g2maurer/PowerMonitor_V7_2/Images/PCB_back.jpg

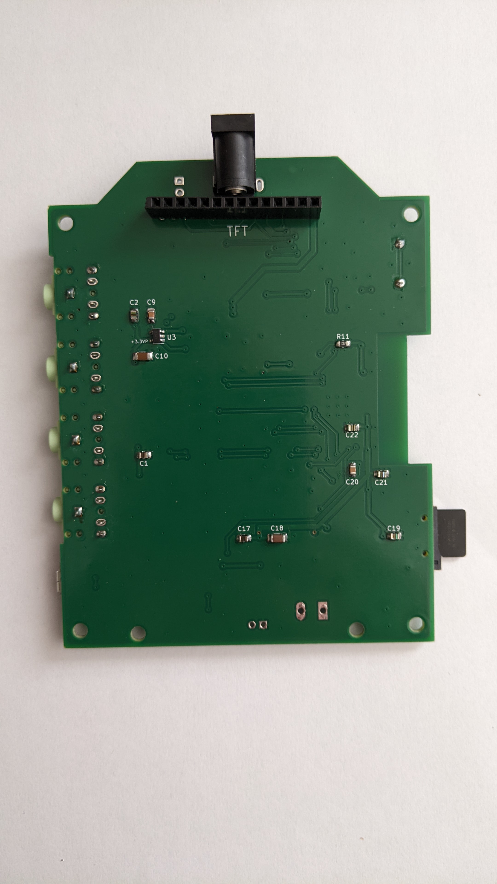
Images/PCB_back.jpg
