g2maurer/PowerMonitor_V7_2/Images/PCB_in_Enclosure.jpg

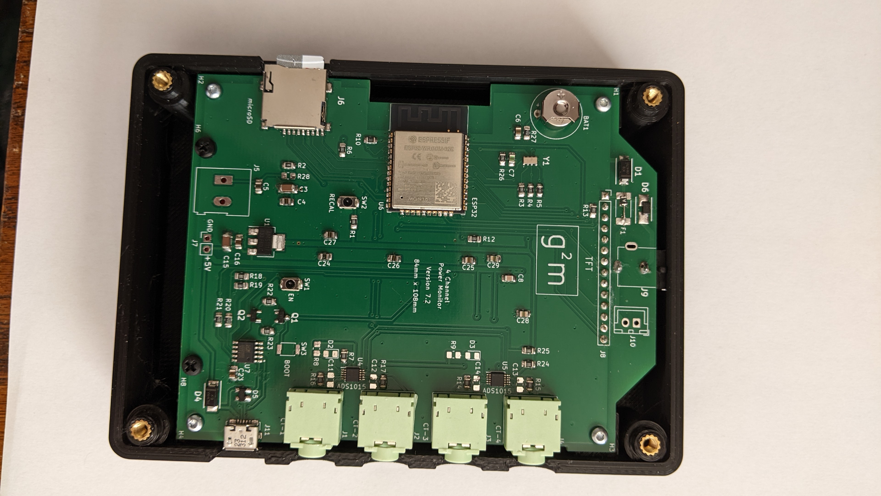
Images/PCB_in_Enclosure.jpg
