g2maurer/PowerMonitor_V7_2/Images/SD_slot.jpg

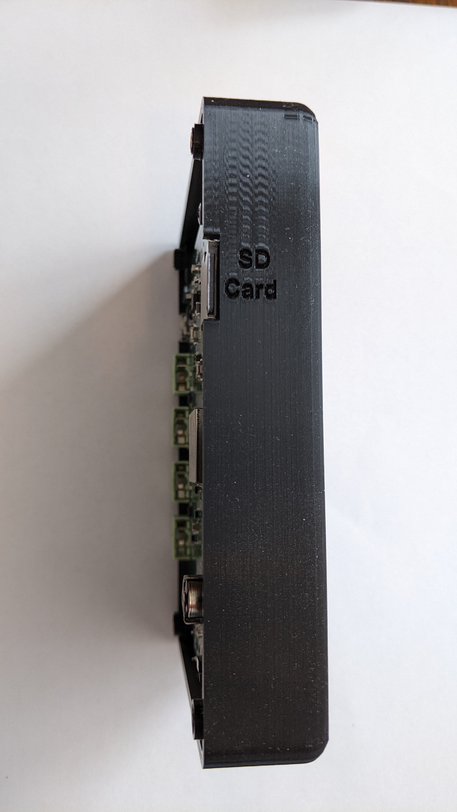
Images/SD_slot.jpg
