g2maurer/PowerMonitor_V7_2/Code/FileHandler.ino

///////////////////////////////////
//
//    Determines whether File exists
//
boolean existsFile(fs::FS &fs, const char *fileName)
{
  return fs.exists(fileName);
}

///////////////////////////////////////////////////////////
//
// Write to the SD card (DON'T MODIFY THIS FUNCTION)
//
//  Example:    writeFile(SD, "/data.txt", "Reading ID, Date, Hour, Temperature \r\n");
//
//
void writeFile(fs::FS &fs, const char * path, const char * message) {
  Serial.printf("Writing file: %s\n", path);

  File file = fs.open(path, FILE_WRITE);
  if(!file) {
    Serial.println("Failed to open file for writing");
    return;
  }
  if(file.print(message)) {
    Serial.println("File written");
  } else {
    Serial.println("Write failed");
  }
  file.close();
}

///////////////////////////////////////////////////////////
//
// Append data to the SD card (DON'T MODIFY THIS FUNCTION)
//
//  Example:    appendFile(SD, "/data.txt", dataMessage.c_str());
//
void appendFile(fs::FS &fs, const char * path, const char * message) {
  Serial.printf("Appending to file: %s\n", path);

  File file = fs.open(path, FILE_APPEND);
  if(!file) {
    Serial.println("Failed to open file for appending");
    Serial.println(path);
    return;
  }
  if(file.print(message)) {
    Serial.println("Message appended");
  } else {
    Serial.println("Append failed");
  }
  file.close();
}

///////////////////////////////////////////////////////////
//
//
//
void renameFile(fs::FS &fs, const char * path1, const char * path2){
    Serial.printf("Renaming file %s to %s\r\n", path1, path2);
    if (fs.rename(path1, path2)) {
        Serial.println("- file renamed");
    } else {
        Serial.println("- rename failed");
    }
}

///////////////////////////////////////////////////////////
//
//
//
void deleteFile(fs::FS &fs, const char * path){
    Serial.printf("Deleting file: %s\r\n", path);
    if(fs.remove(path)){
        Serial.println("- file deleted");
    } else {
        Serial.println("- delete failed");
    }
}

////////////////////////////////////////////////////
//
//    List files in directory
//
//    Example:
//      listDir(SPIFFS, "/", 0);
//      listDir(SD, "/", 0);
//
void listDir(fs::FS &fs, const char * dirname, uint8_t levels){
    Serial.printf("Listing directory: %s\n", dirname);

    File root = fs.open(dirname);
    if(!root){
        Serial.println("Failed to open directory");
        return;
    }
    if(!root.isDirectory()){
        Serial.println("Not a directory");
        return;
    }

    File file = root.openNextFile();
    while(file){
        if(file.isDirectory()){
            Serial.print("  DIR : ");
            Serial.print (file.name());
            time_t t= file.getLastWrite();
            struct tm * tmstruct = localtime(&t);
            Serial.printf("  LAST WRITE: %d-%02d-%02d %02d:%02d:%02d\n",(tmstruct->tm_year)+1900,( tmstruct->tm_mon)+1, tmstruct->tm_mday,tmstruct->tm_hour , tmstruct->tm_min, tmstruct->tm_sec);
            if(levels){
                listDir(fs, file.path(), levels -1);
            }
        } else {
            Serial.print("  FILE: ");
            Serial.print(file.name());
            Serial.print("  SIZE: ");
            Serial.print(file.size());
            time_t t= file.getLastWrite();
            struct tm * tmstruct = localtime(&t);
            Serial.printf("  LAST WRITE: %d-%02d-%02d %02d:%02d:%02d\n",(tmstruct->tm_year)+1900,( tmstruct->tm_mon)+1, tmstruct->tm_mday,tmstruct->tm_hour , tmstruct->tm_min, tmstruct->tm_sec);
        }
        file = root.openNextFile();
    }
}
